Jana-Marie/OtterCam-s3/images/2.jpg

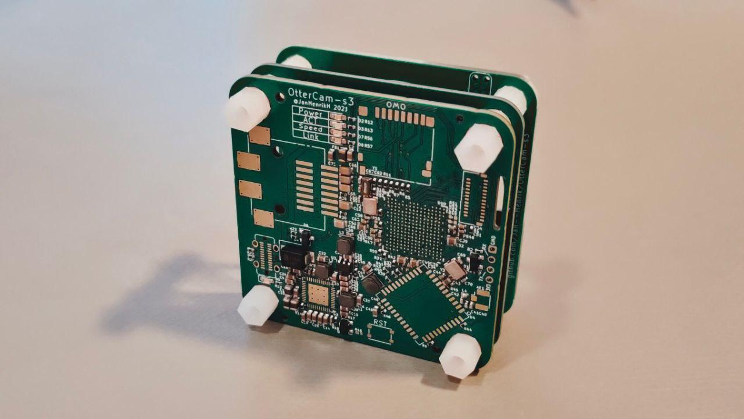
images/2.jpg
