Jana-Marie/OtterCam-s3/images/3.jpg

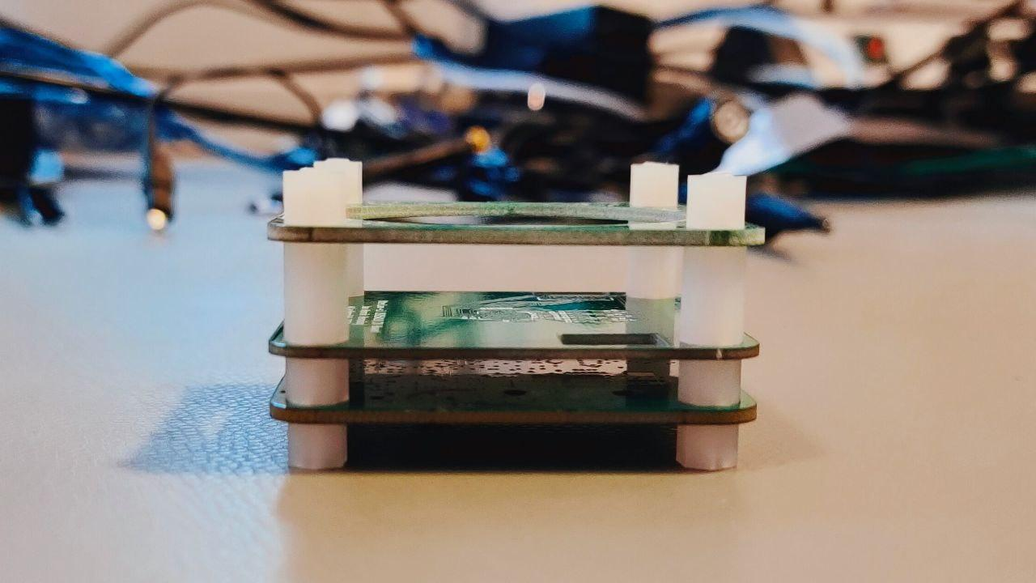
images/3.jpg
